kenny-caldieraro/Sliders-timer-replica/PICTURES/IMG_0773.jpg

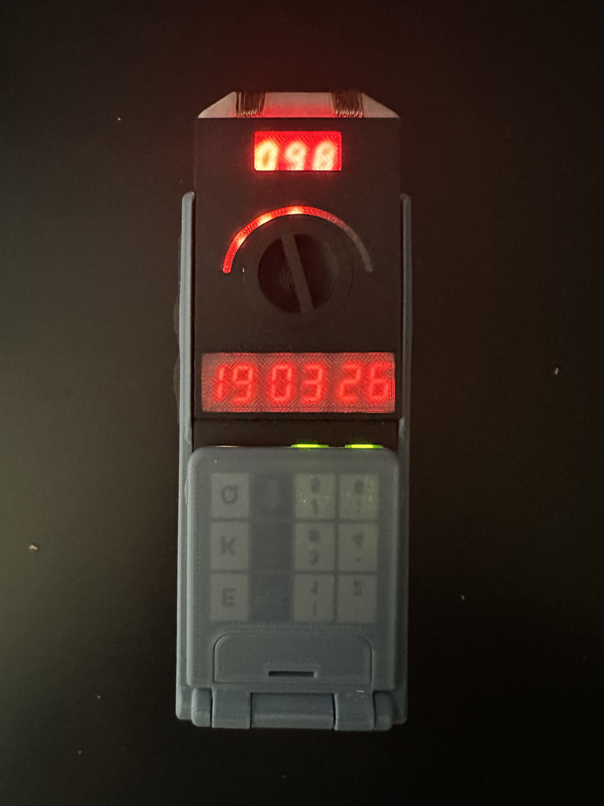
PICTURES/IMG_0773.jpg
