kenny-caldieraro/Sliders-timer-replica/PICTURES/IMG_0775.jpg

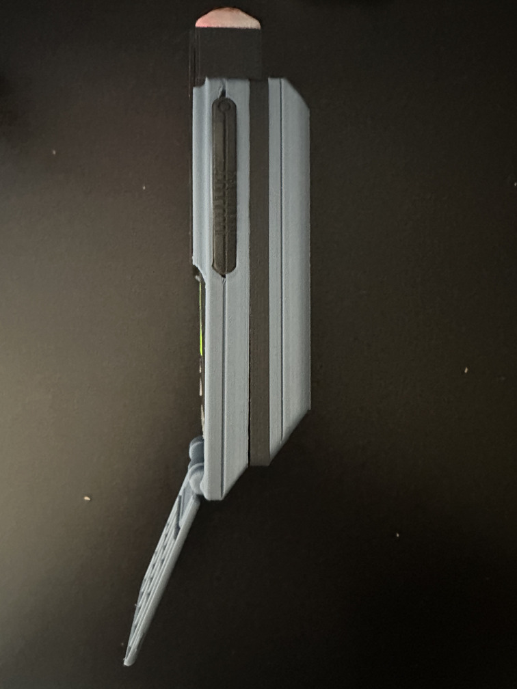
PICTURES/IMG_0775.jpg
