kenny-caldieraro/Sliders-timer-replica/PICTURES/IMG_0776.jpg

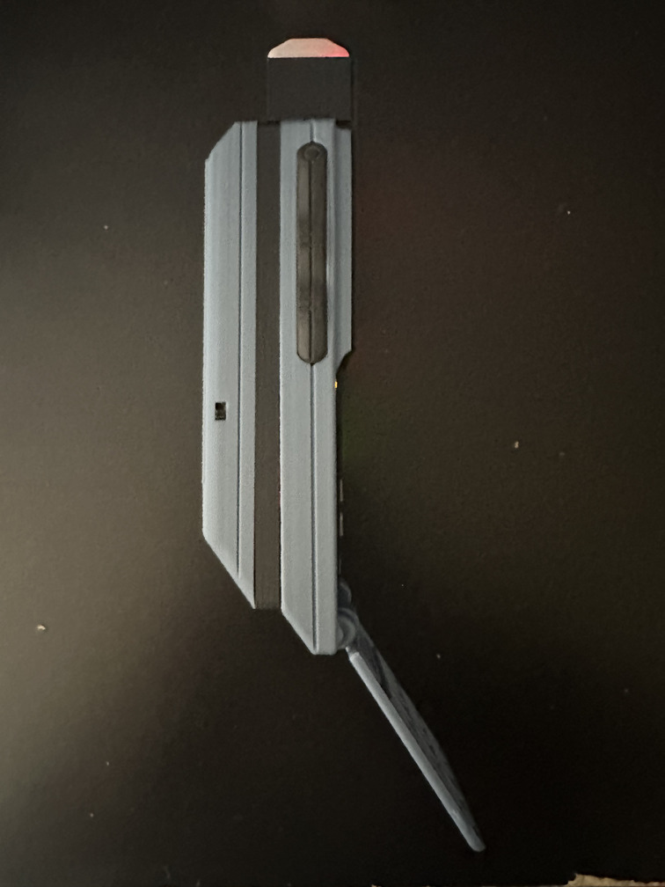
PICTURES/IMG_0776.jpg
