kenny-caldieraro/Sliders-timer-replica/PICTURES/IMG_0777.jpg

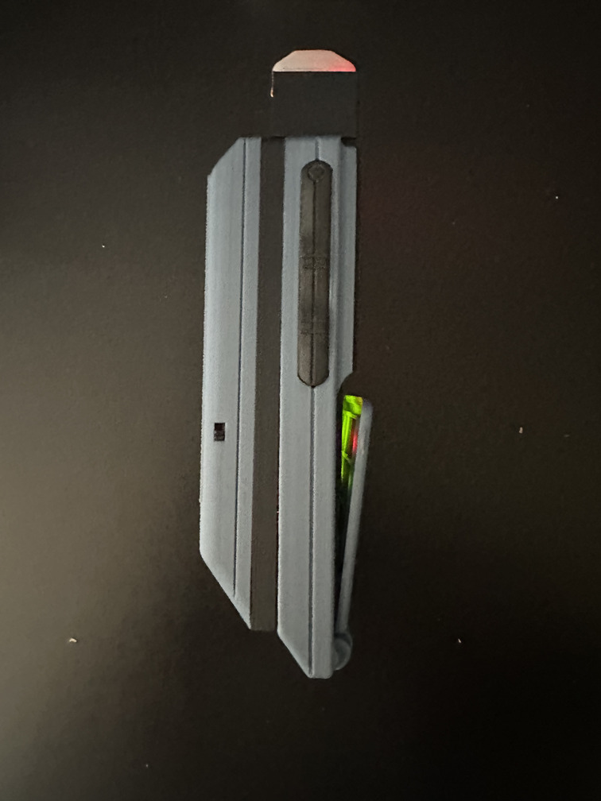
PICTURES/IMG_0777.jpg
