kenny-caldieraro/Sliders-timer-replica/PICTURES/IMG_0778.jpg

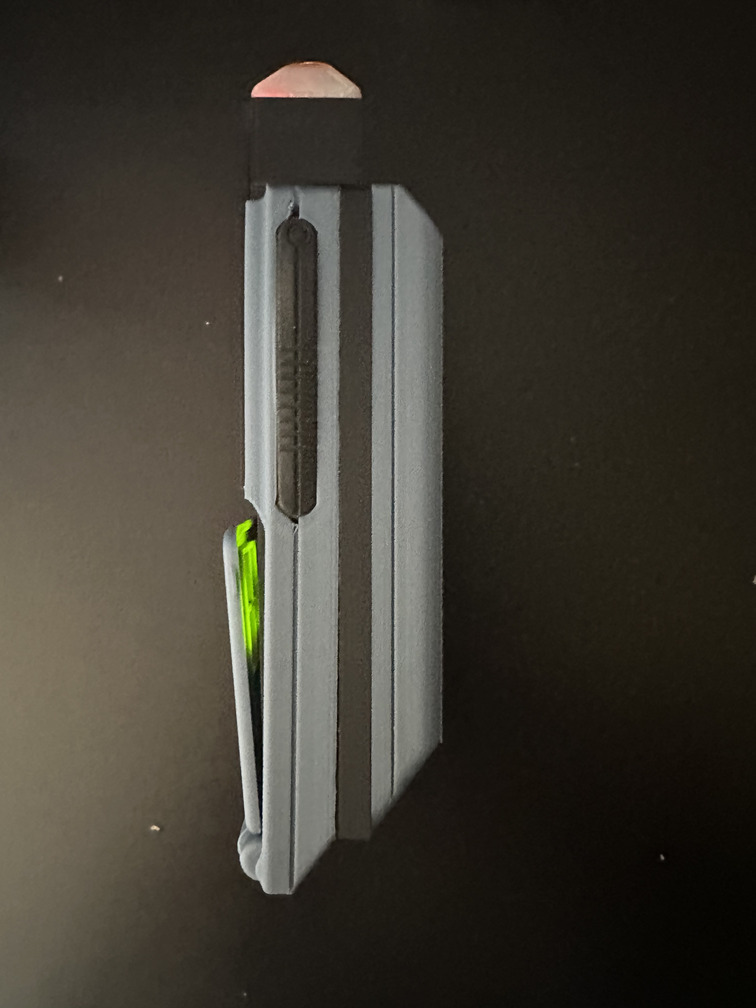
PICTURES/IMG_0778.jpg
