kenny-caldieraro/Sliders-timer-replica/PICTURES/IMG_0779.jpg

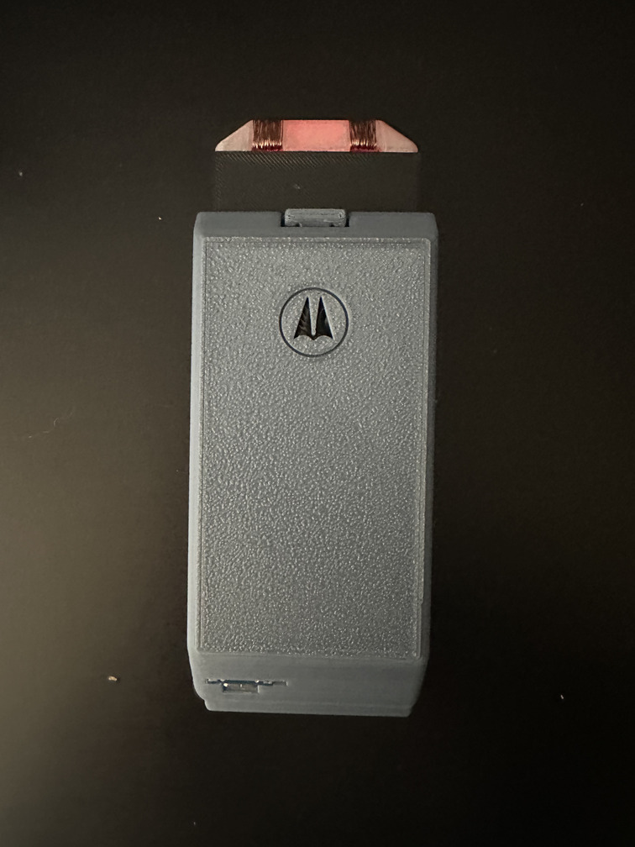
PICTURES/IMG_0779.jpg
