kenny-caldieraro/Sliders-timer-replica/PICTURES/INSPIRATION/IMG_20200306_144748.jpg

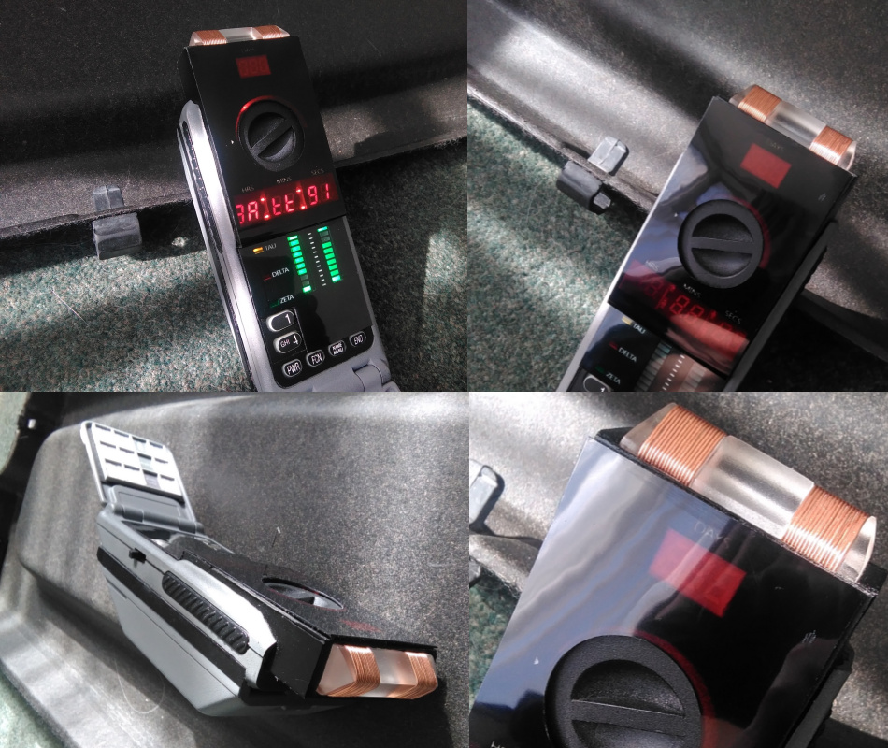
PICTURES/INSPIRATION/IMG_20200306_144748.jpg
