kenny-caldieraro/Sliders-timer-replica/PICTURES/INSPIRATION/IMG_20200306_145352.jpg

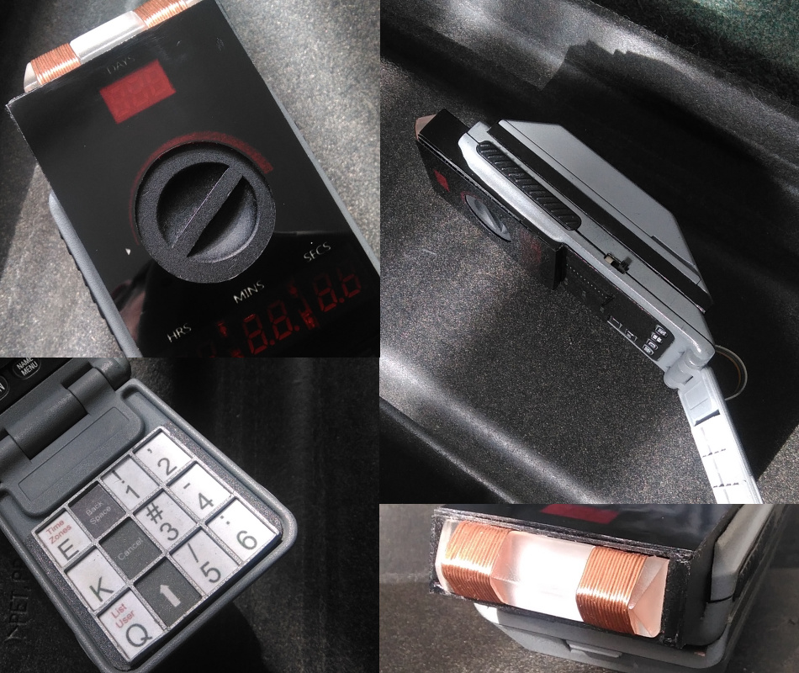
PICTURES/INSPIRATION/IMG_20200306_145352.jpg
