kenny-caldieraro/Sliders-timer-replica/PICTURES/INSPIRATION/IMG_20200306_150910.jpg

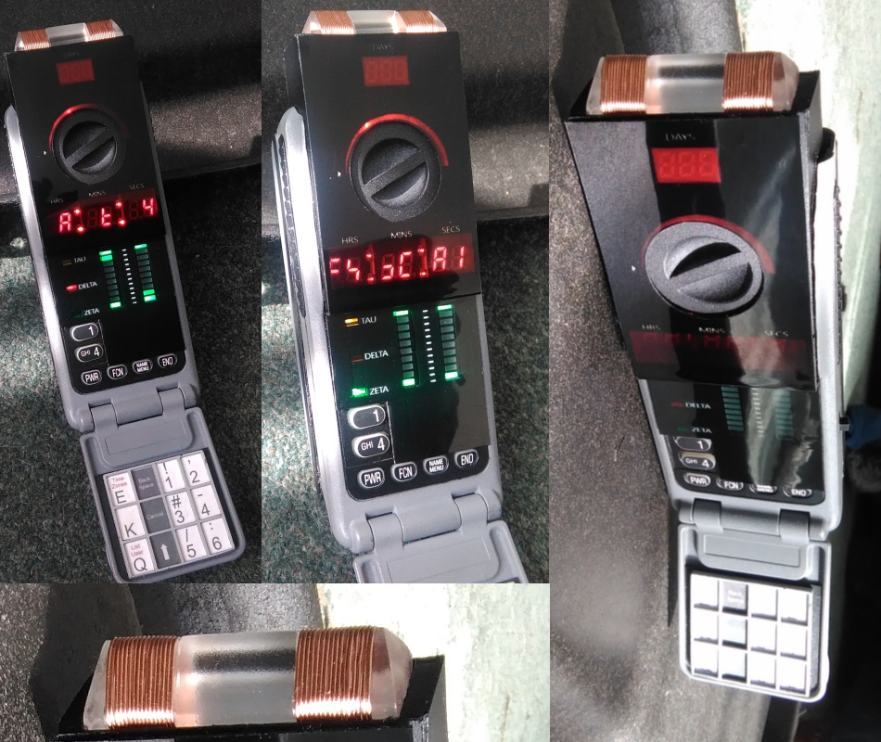
PICTURES/INSPIRATION/IMG_20200306_150910.jpg
