kenny-caldieraro/Sliders-timer-replica/PICTURES/INSPIRATION/IMG_20200306_152816.jpg

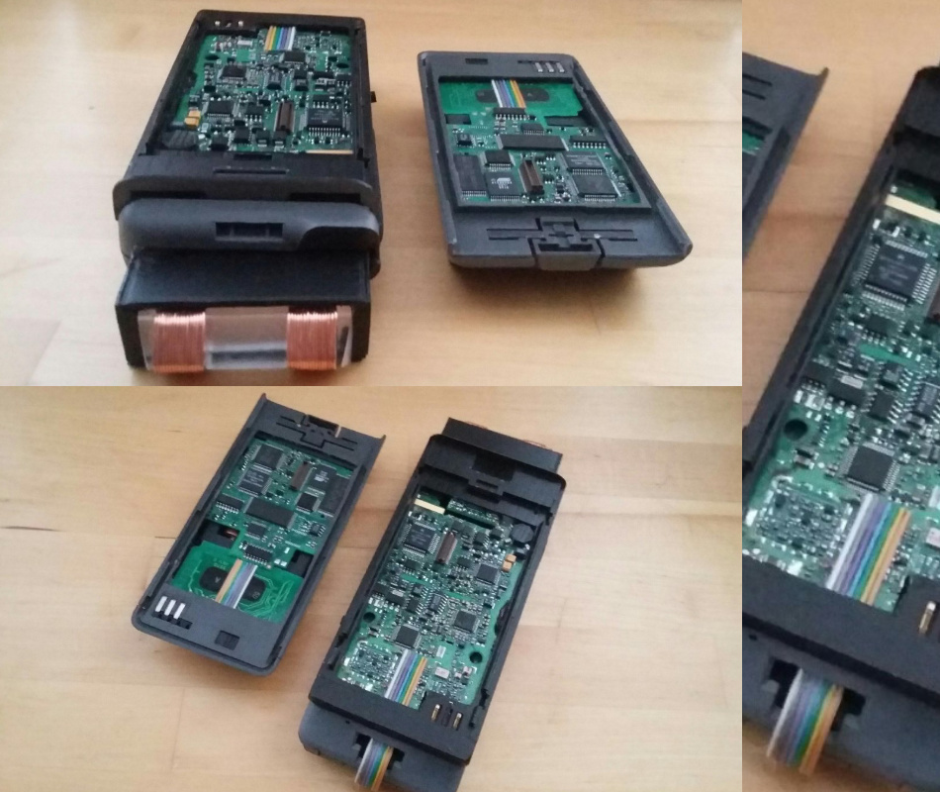
PICTURES/INSPIRATION/IMG_20200306_152816.jpg
