kenny-caldieraro/Sliders-timer-replica/PICTURES/INSPIRATION/IMG_20200306_153102.jpg

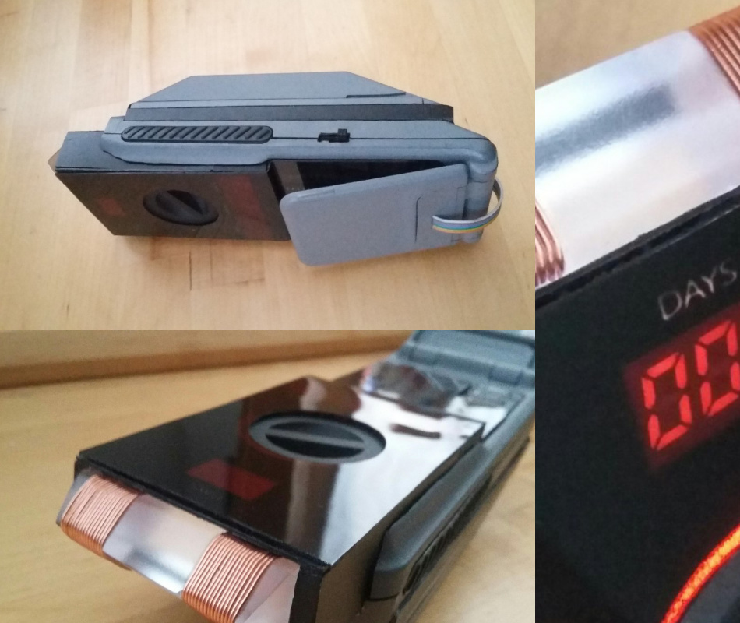
PICTURES/INSPIRATION/IMG_20200306_153102.jpg
