kenny-caldieraro/Sliders-timer-replica/STL/IMAGES/Battery_box v1.jpg

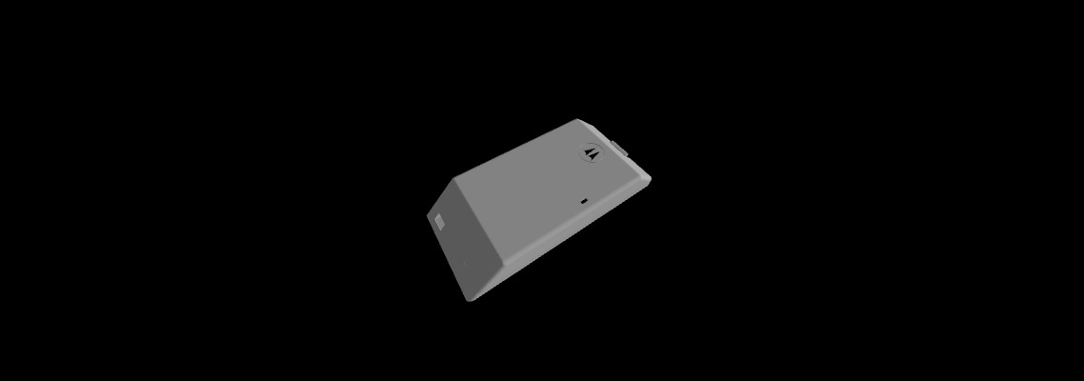
STL/IMAGES/Battery_box v1.jpg
