kenny-caldieraro/Sliders-timer-replica/STL/IMAGES/Button_plate v1.jpg

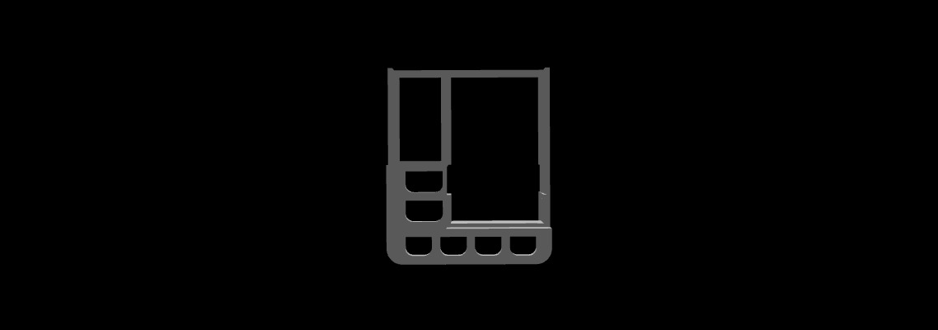
STL/IMAGES/Button_plate v1.jpg
