kenny-caldieraro/Sliders-timer-replica/STL/IMAGES/Buttons.jpg

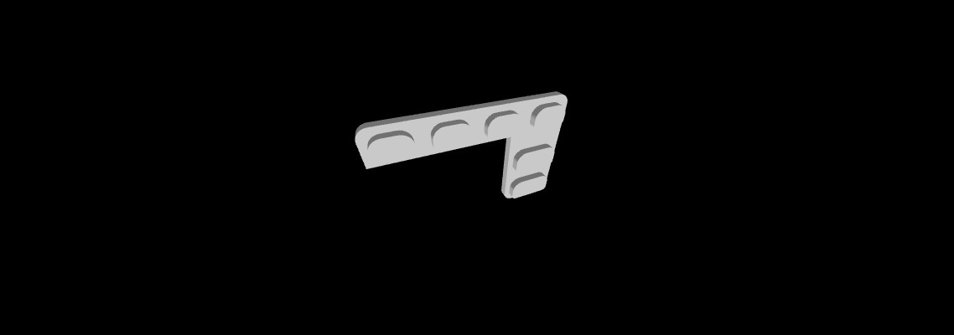
STL/IMAGES/Buttons.jpg
